Beaupre-Circuit-Design/c64-composite-modulator/images/C64-Composite-Modulator-Bottom-Unpopulated.png

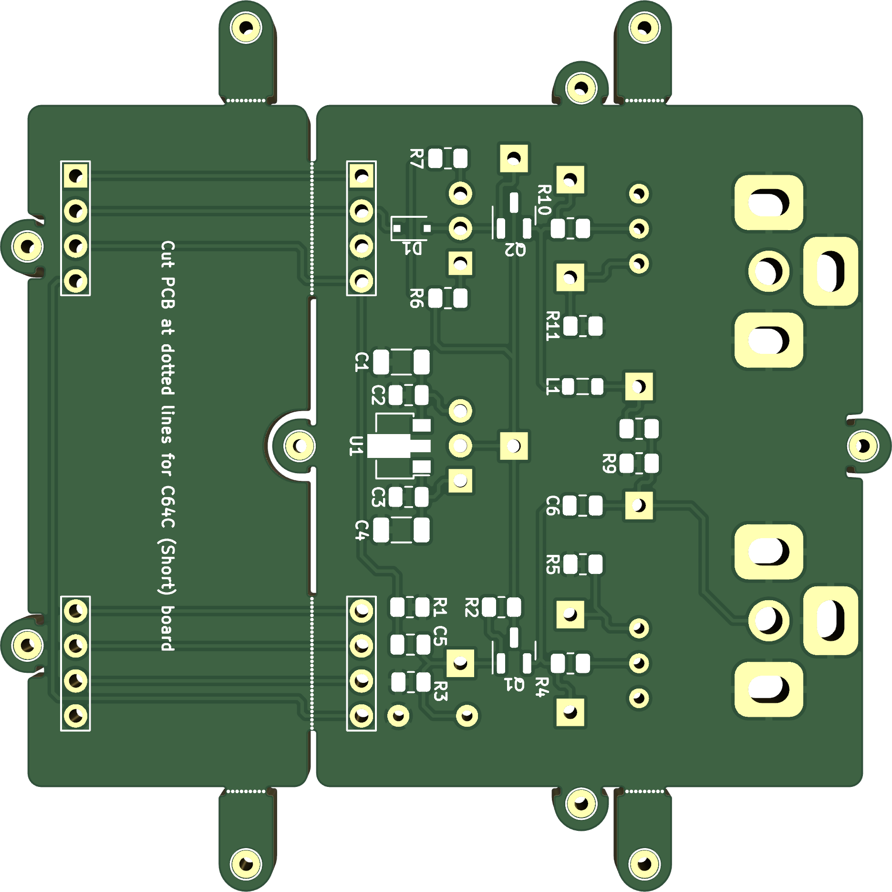
images/C64-Composite-Modulator-Bottom-Unpopulated.png
