Beaupre-Circuit-Design/c64-composite-modulator/images/C64-Composite-Modulator-Top-Unpopulated_Small.png

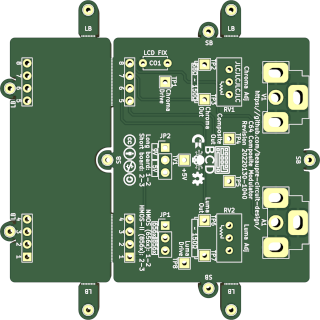
images/C64-Composite-Modulator-Top-Unpopulated_Small.png
